sibbl08/Climbing-Robot/Mujoco/meshes/ankle_link_r.stl

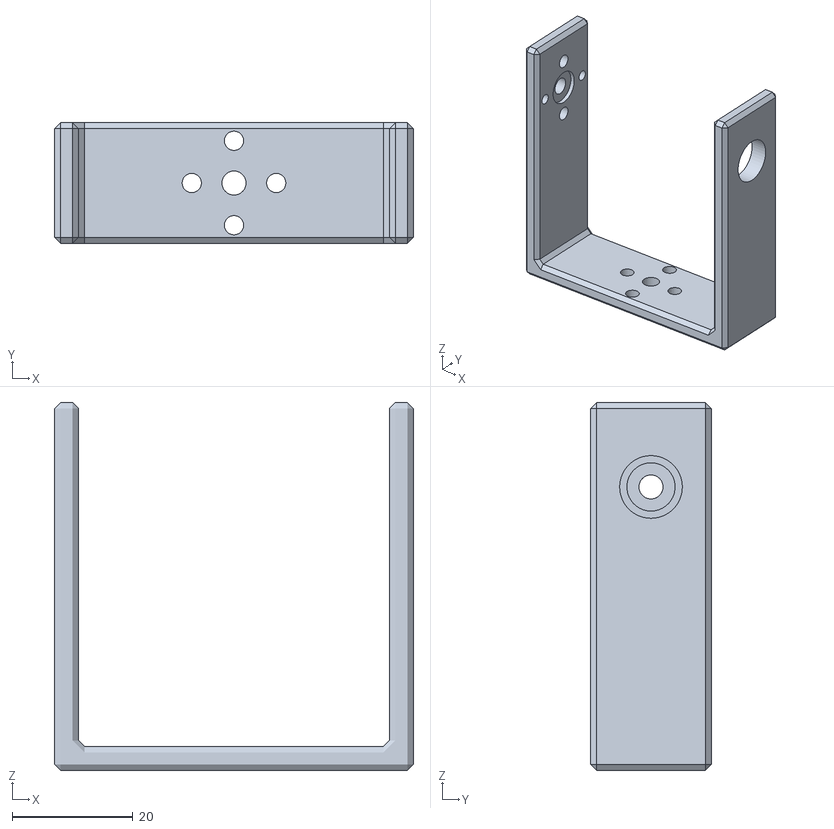
[picture p24: CAD file, 2025-11-30]
Mujoco/meshes/ankle_link_r.stl
59.5 x 20.0 x 61.0
