sibbl08/Climbing-Robot/Mujoco/meshes/foot_r.stl

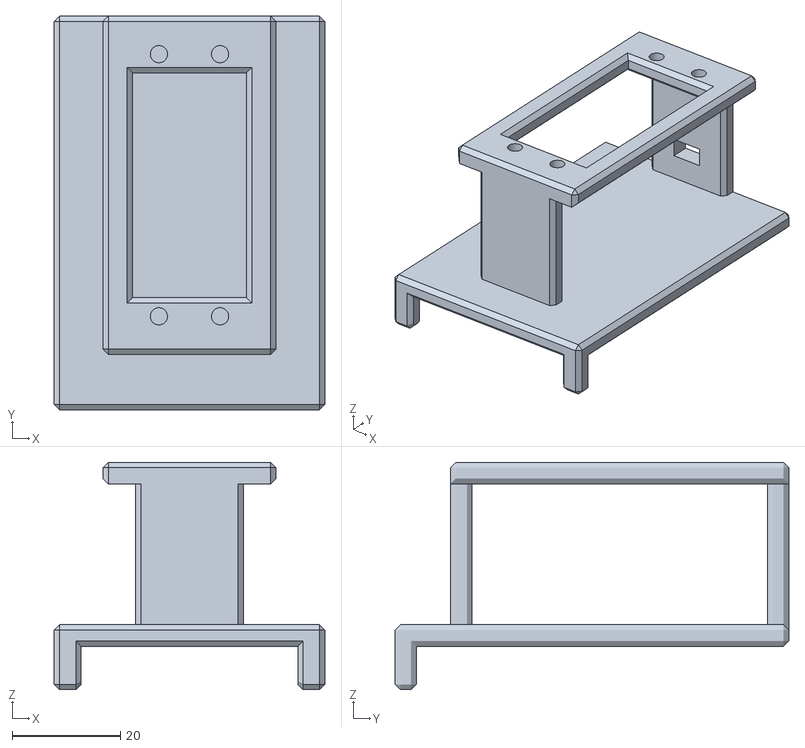
[picture p25: CAD file, 2025-11-30]
Mujoco/meshes/foot_r.stl
50.0 x 72.8 x 42.0
