sibbl08/Climbing-Robot/Mujoco/meshes/Chest.stl

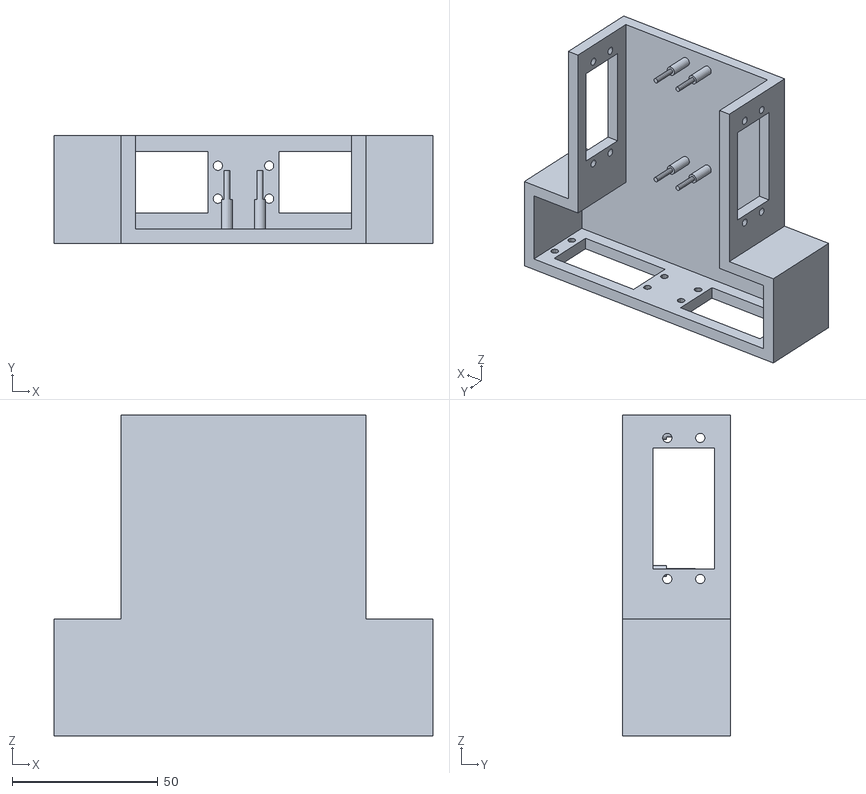
[picture p26: CAD file, 2025-11-30]
Mujoco/meshes/Chest.stl
130.0 x 37.0 x 110.0
